antaramazumdar/3D-scanner/PIE_MP2_schematics/PIE_MP2_schematics.kicad_sch

## KiCad design PIE_MP2_schematics/PIE_MP2_schematics.kicad_sch (2025-09-26)

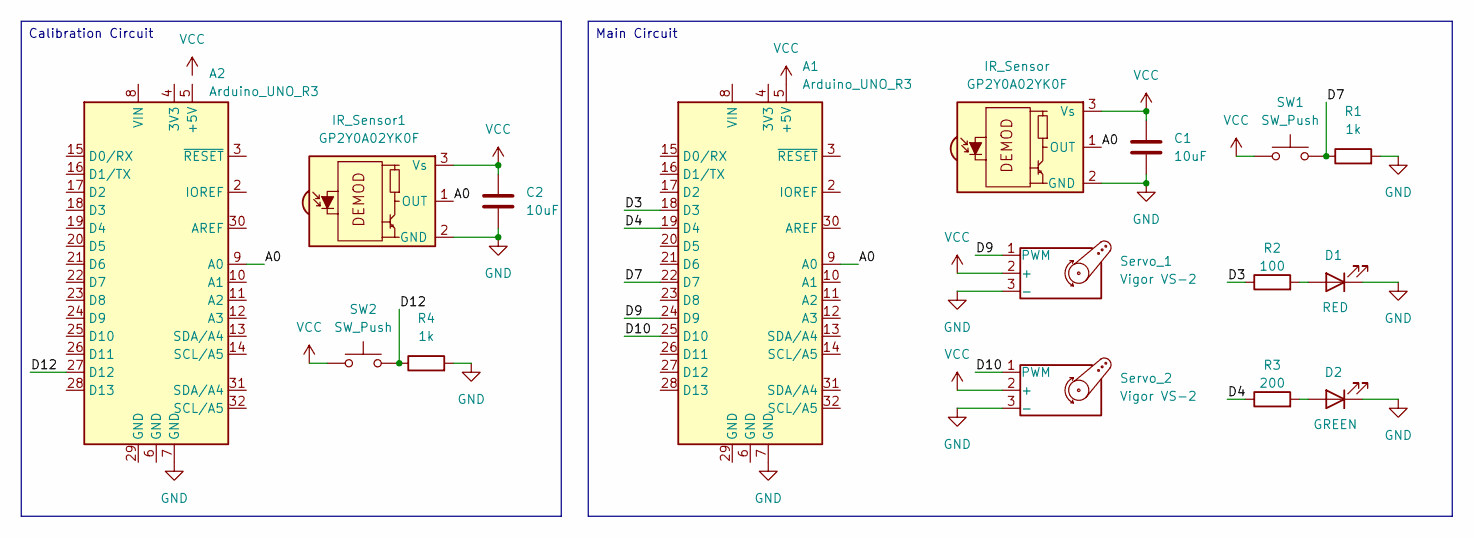
[picture p1: schematic PIE_MP2_schematics.kicad_sch]

Parts:
A1, A2: Arduino_UNO_R3
C1, C2: 10uF
D1: RED
D2: GREEN
IR_Sensor, IR_Sensor1: GP2Y0A02YK0F; Vishay_MINICAST-3Pin
R1, R4: 1k
R2: 100
R3: 200
SW1, SW2: SW_Push
Servo_1, Servo_2: Vigor VS-2

Connections:
A0: A1.9 (A0), A2.9 (A0), IR_Sensor.1 (OUT), IR_Sensor1.1 (OUT)
D3: A1.18 (D3), R2.1
D4: A1.19 (D4), R3.1
D7: A1.22 (D7), R1.1, SW1.2
D9: A1.24 (D9), Servo_1.1 (PWM)
D10: A1.25 (D10), Servo_2.1 (PWM)
D12: A2.27 (D12), R4.1, SW2.2
GND: A1.7 (GND), A2.7 (GND), C1.2, C2.2, D1.1 (K), D2.1 (K), IR_Sensor.2 (GND), IR_Sensor1.2 (GND), R1.2, R4.2, Servo_1.3 (-), Servo_2.3 (-)
unnamed: D1.2 (A), R2.2
unnamed: D2.2 (A), R3.2
VCC: A1.5 (+5V), C1.1, C2.1, IR_Sensor.3 (Vs), IR_Sensor1.3 (Vs), SW1.1, SW2.1, Servo_1.2 (+), Servo_2.2 (+)

Notes on the sheet:
Main Circuit
Calibration Circuit
